deviputridev/DSIOT_ILMAS_1/images_/landing page.png

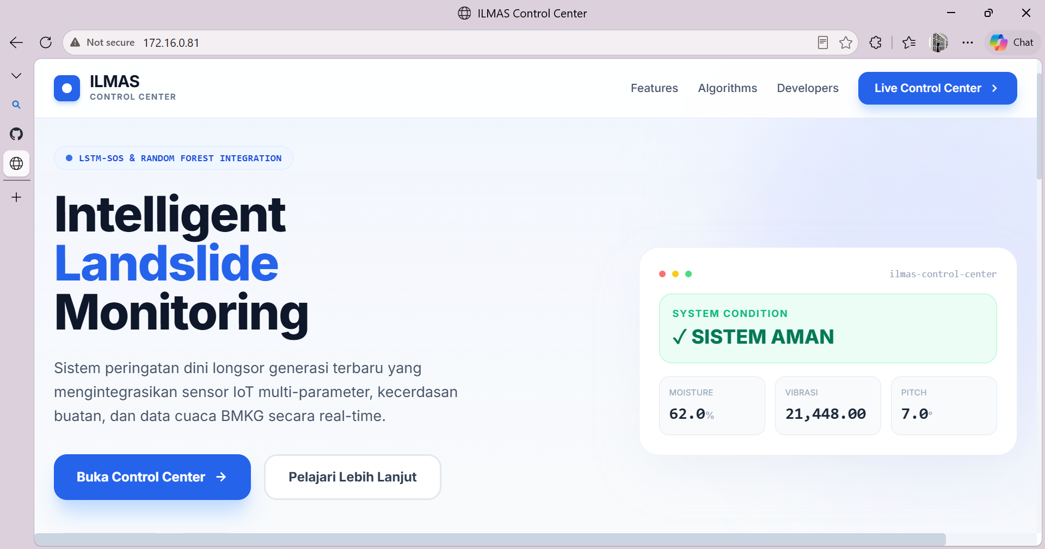
images_/landing page.png
